roblatour/esp32max7219/esp32max7219/pushbulletCertificates.h

// ESP32 Message Board v2.3
// Copyright Rob Latour, 2025

// To get the certificates, as coded below, you can use the  program for Windows called 'Certifiable'
// For more information and/or to download the program please visit: https://github.com/roblatour/certifiable
//
// note: at the time the code below was written api.pushbullet.com and zebra.pushbullet.com were using the same certificate but they are kept separate below in case they change in the future
//

const char *PUSHBULLET_API_HOST = "api.pushbullet.com";
const uint16_t PUSHBULLET_SERVER_PORT = 443;

// The following code is for use with api.pushbullet.com:443
//
// It has been generated by Certifiable v1.5 ( https://github.com/roblatour/certifiable ) using the following command:
// "C:\Program Files\certifiable\certifiable.exe" api.pushbullet.com -g c++ progmem -n 2 -v API_PUSHBULLET_COM_CERTIFICATE -c
//
// The certificate below is valid between 2024-03-12 20:00:00 (UTC) and 2027-03-12 18:59:59 (UTC) inclusive
//
static const char *API_PUSHBULLET_COM_CERTIFICATE PROGMEM = R"EOF(
-----BEGIN CERTIFICATE-----
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
Ig46v9mFmBvyH04=
-----END CERTIFICATE-----
)EOF";

//
//

const char *PUSHBULLET_KEEP_ALIVE_HOST = "zebra.pushbullet.com";
const uint16_t PUSHBULLET_KEEP_ALIVE_PORT = 443;

// The following code is for use with zebra.pushbullet.com:443
//
// It has been generated by Certifiable v1.5 ( https://github.com/roblatour/certifiable ) using the following command:
// "C:\Program Files\certifiable\certifiable.exe" zebra.pushbullet.com -g c++ progmem -n 2 -v ZEBRA_PUSHBULLET_COM_CERTIFICATE -c
//
// The certificate below is valid between 2024-03-12 20:00:00 (UTC) and 2027-03-12 18:59:59 (UTC) inclusive
//
static const char *ZEBRA_PUSHBULLET_COM_CERTIFICATE PROGMEM = R"EOF(
-----BEGIN CERTIFICATE-----
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
Ig46v9mFmBvyH04=
-----END CERTIFICATE-----
)EOF";
